timtashpulatov/ok240/3d/FloppyFrame.FCStd

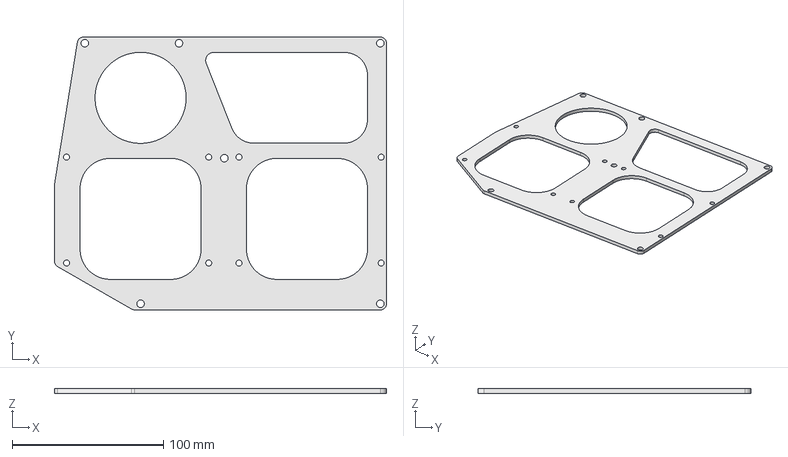
[picture p17: CAD file, 2025-06-13]
3d/FloppyFrame.FCStd
219.5 x 180.3 x 3.00 mm
