timtashpulatov/ok240/3d/FDC.FCStd

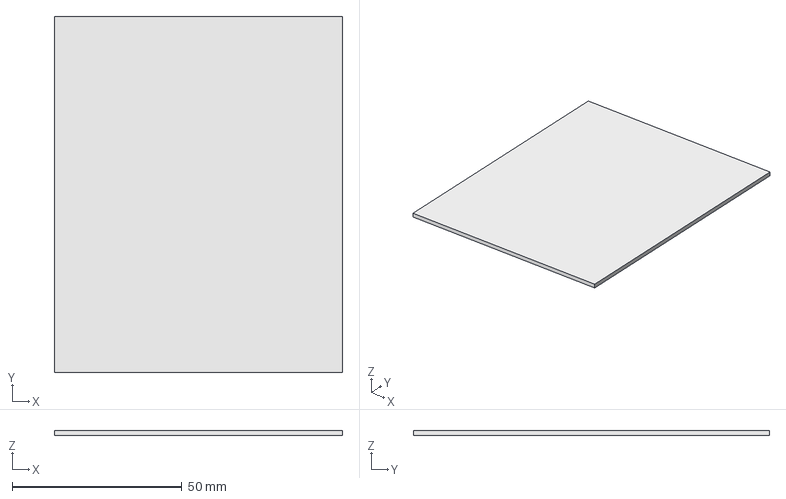
[picture p18: CAD file, 2025-06-05]
3d/FDC.FCStd
85.0 x 105.0 x 1.60 mm
