timtashpulatov/ok240/3d/PCB.FCStd

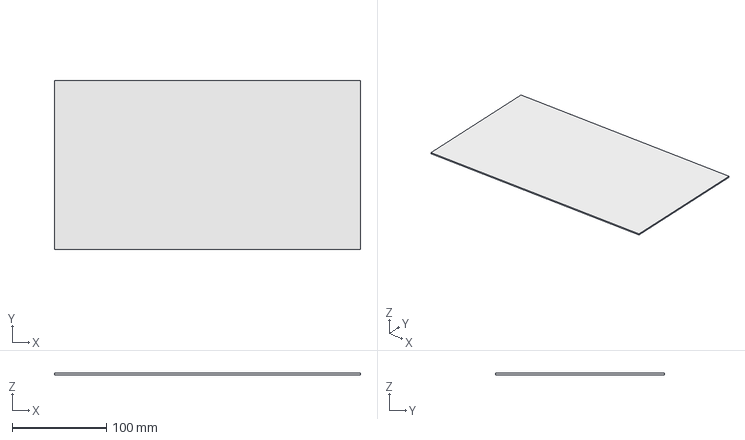
[picture p19: CAD file, 2025-06-01]
3d/PCB.FCStd
325.0 x 180.0 x 1.60 mm
