timtashpulatov/ok240/io.asm

        .project io
        .org    100h
 
 ; Read from or write to IO port
        lxi     h, 80h  ; FCB
 
        mov     a, m
        cpi     1
        jnc     PortAddr

;        jmp     0b422h  ; CP/M 2.2 REL.8 commerr1 routine

        lxi     d, Help
        mvi     c, 9
        jmp     5
Help:   db      'IO v0.2', 10, 13
        db      'Usage: IO PP - read from port PP', 10, 13
        db      '       IO PP DD - write DD to port PP', 10, 13, '$'

PortAddr:
        inx     h       ; FCB+1
        inx     h       ; FCB+2
        call    ConvertParam    ; 1st param first byte
        sta     Work+3

PortData:
        inx     h       ; FCB+4
        inx     h       ; FCB+5
        call    ConvertParam    ; 2nd param first byte
        sta     Work+1
        
        lda     80h     ; FCB
        cpi     3
        jz      Work

Write:
        mvi     a, 0d3h
        sta     Work+2

Work:        
        mvi     a, 00
        in      00
        ; jmp     0e003h

        push    psw
        rrc
        rrc
        rrc
        rrc
        call    PrintNibble
        pop     psw
        ; jmp     PrintNibble


PrintNibble:
        ani     0fh
        adi     '0'
        cpi     03ah
        jc      $+5
        adi     7
        mov     e, a
        mvi     c, 2    ; Console Output
        jmp     5
        




ConvertParam:
        call    ConvertNibble
        rlc
        rlc
        rlc
        rlc
        mov     c, a
        
        inx     h
        call    ConvertNibble
        ora     c
        ret

ConvertNibble:
        mov     a, m
        sui     '0'
        cpi     10
        rc
        sui     7
        ret
        
